averagejmc/HomeSecurity/arduino-code/main/esp01/MqttHandler.h

#ifndef MQTTCLIENT_H
#define MQTTCLIENT_H

#include <ESP8266WiFi.h>
#include <PubSubClient.h>

class MQTTClientHandler {
public:
    MQTTClientHandler(const char* ssid, const char* password, const char* server, uint16_t port = 1883);
    
    void begin();
    void connectWifi();
    void loop();
    void publish(const char* topic, const char* message);
    
private:
    void reconnect();

    const char* ssid;
    const char* password;
    const char* server;
    uint16_t port;

    WiFiClient espClient;
    PubSubClient client;

    unsigned long lastReconnectAttempt = 0;
    const unsigned long reconnectInterval = 1000;
};

#endif
